HowlandH/RAD-Gait-Analysis/gait_tracker/power_mgmt.cpp

/*
 * Power Management Module - Implementation
 *
 * Handles battery monitoring and low-power modes
 */

#include "power_mgmt.h"
#include "config.h"

void initPowerManagement() {
  // Set up battery monitoring pin
  pinMode(BATTERY_PIN, INPUT);

  Serial.println("Power management initialized");
}

uint8_t getBatteryPercent() {
  float voltage = getBatteryVoltage();

  // Map voltage to percentage (3.0V = 0%, 4.2V = 100%)
  float percent = (voltage - BATTERY_EMPTY_VOLTAGE) /
                  (BATTERY_FULL_VOLTAGE - BATTERY_EMPTY_VOLTAGE) * 100.0;

  // Clamp to 0-100 range
  if (percent < 0) percent = 0;
  if (percent > 100) percent = 100;

  return (uint8_t)percent;
}

float getBatteryVoltage() {
  // Read analog value (0-1023 for 10-bit ADC)
  int rawValue = analogRead(BATTERY_PIN);

  // Convert to voltage (assuming 3.3V reference)
  float voltage = (rawValue / 1023.0) * 3.3;

  // Apply voltage divider ratio to get actual battery voltage
  voltage = voltage / BATTERY_VOLTAGE_RATIO;

  if (DEBUG_MODE) {
    // Uncomment for debugging
    // Serial.print("Battery voltage: ");
    // Serial.print(voltage, 2);
    // Serial.println(" V");
  }

  return voltage;
}

void enterLowPowerMode() {
  Serial.println("Entering low-power mode...");

  // TODO: Implement actual low-power mode
  /*
  // Actual implementation would:
  // 1. Reduce BLE advertising interval
  // 2. Lower IMU sampling rate
  // 3. Disable LEDs
  // 4. Enable MPU-6050 motion interrupt
  // 5. Put processor in low-power state

  // For Arduino Nano 33 BLE:
  // - Use ArduinoLowPower library
  // - Configure MPU-6050 interrupt to wake on motion
  */

  Serial.println("Low-power mode active. Wake on motion.");
}

void wakeFromMotion() {
  Serial.println("Waking from low-power mode...");

  // TODO: Implement wake-up routine
  /*
  // Actual implementation would:
  // 1. Resume normal BLE advertising
  // 2. Restore normal IMU sampling rate
  // 3. Clear motion interrupt flag
  */

  Serial.println("Device active");
}
